guidoschreuder/zebus/zebus/src/zebus-secrets-sample.h

#ifndef ZEBUS_SECRETS_H
#define ZEBUS_SECRETS_H

#define ZEBUS_TELEGRAM_TOKEN "xxxxxxxx:xxxxxxxxxxx-xxxxxxxxxxxxxxxxxxxx"
#define ZEBUS_TELEGRAM_CLIENT_ID 1234567890

#define ZEBUS_MQTT_USERNAME "mqtt-username"
#define ZEBUS_MQTT_PASSWORD "mqtt-password"

#endif
